ph-design/PH60Slim-Choc/Image/002.jpg

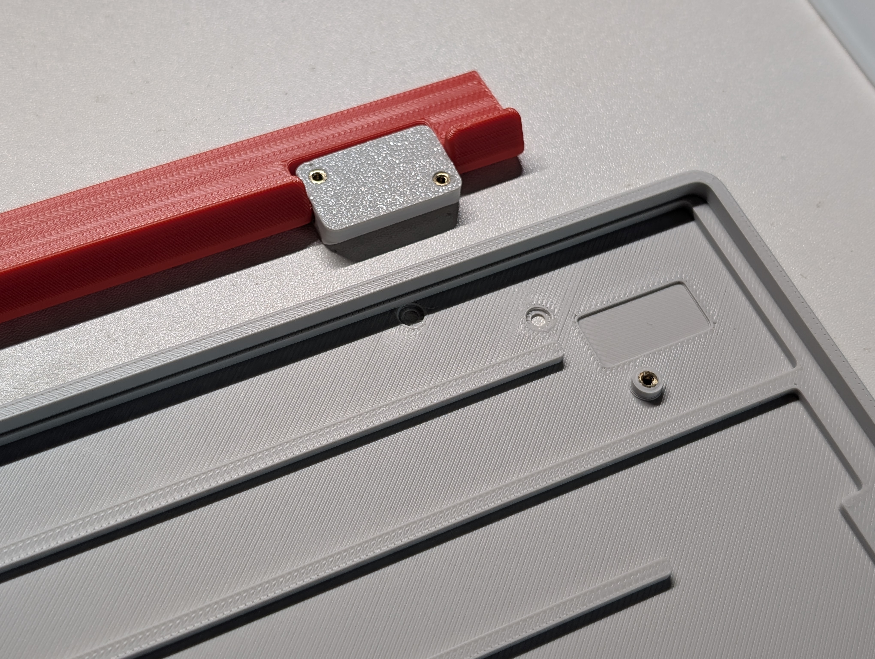
Image/002.jpg
