ph-design/PH60Slim-Choc/Image/009.jpg

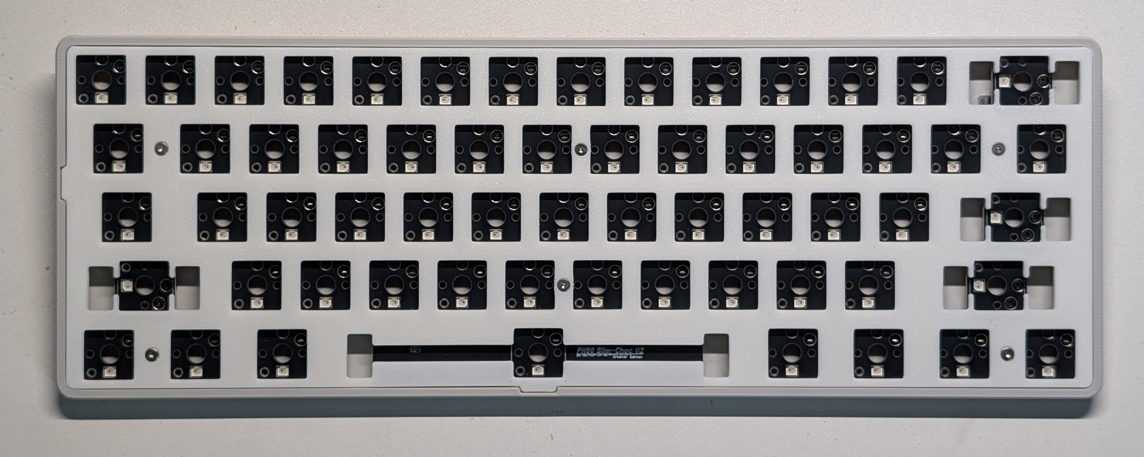
Image/009.jpg
