ph-design/PH60Slim-Choc/Image/010.jpg

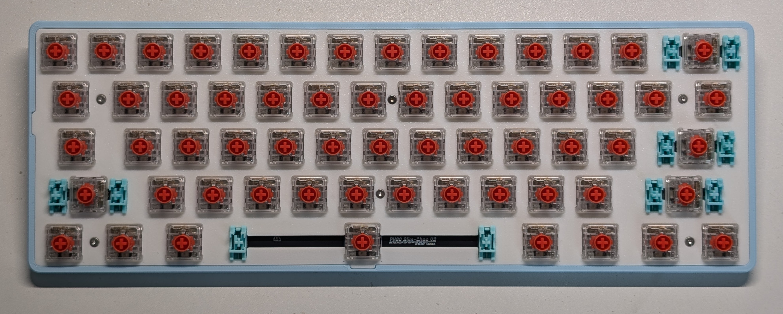
Image/010.jpg
