ph-design/PH60Slim-Choc/PCB/Rev1/PH60Slim-Choc.kicad_sch

## KiCad design PCB/Rev1/PH60Slim-Choc.kicad_sch (2025-04-30)

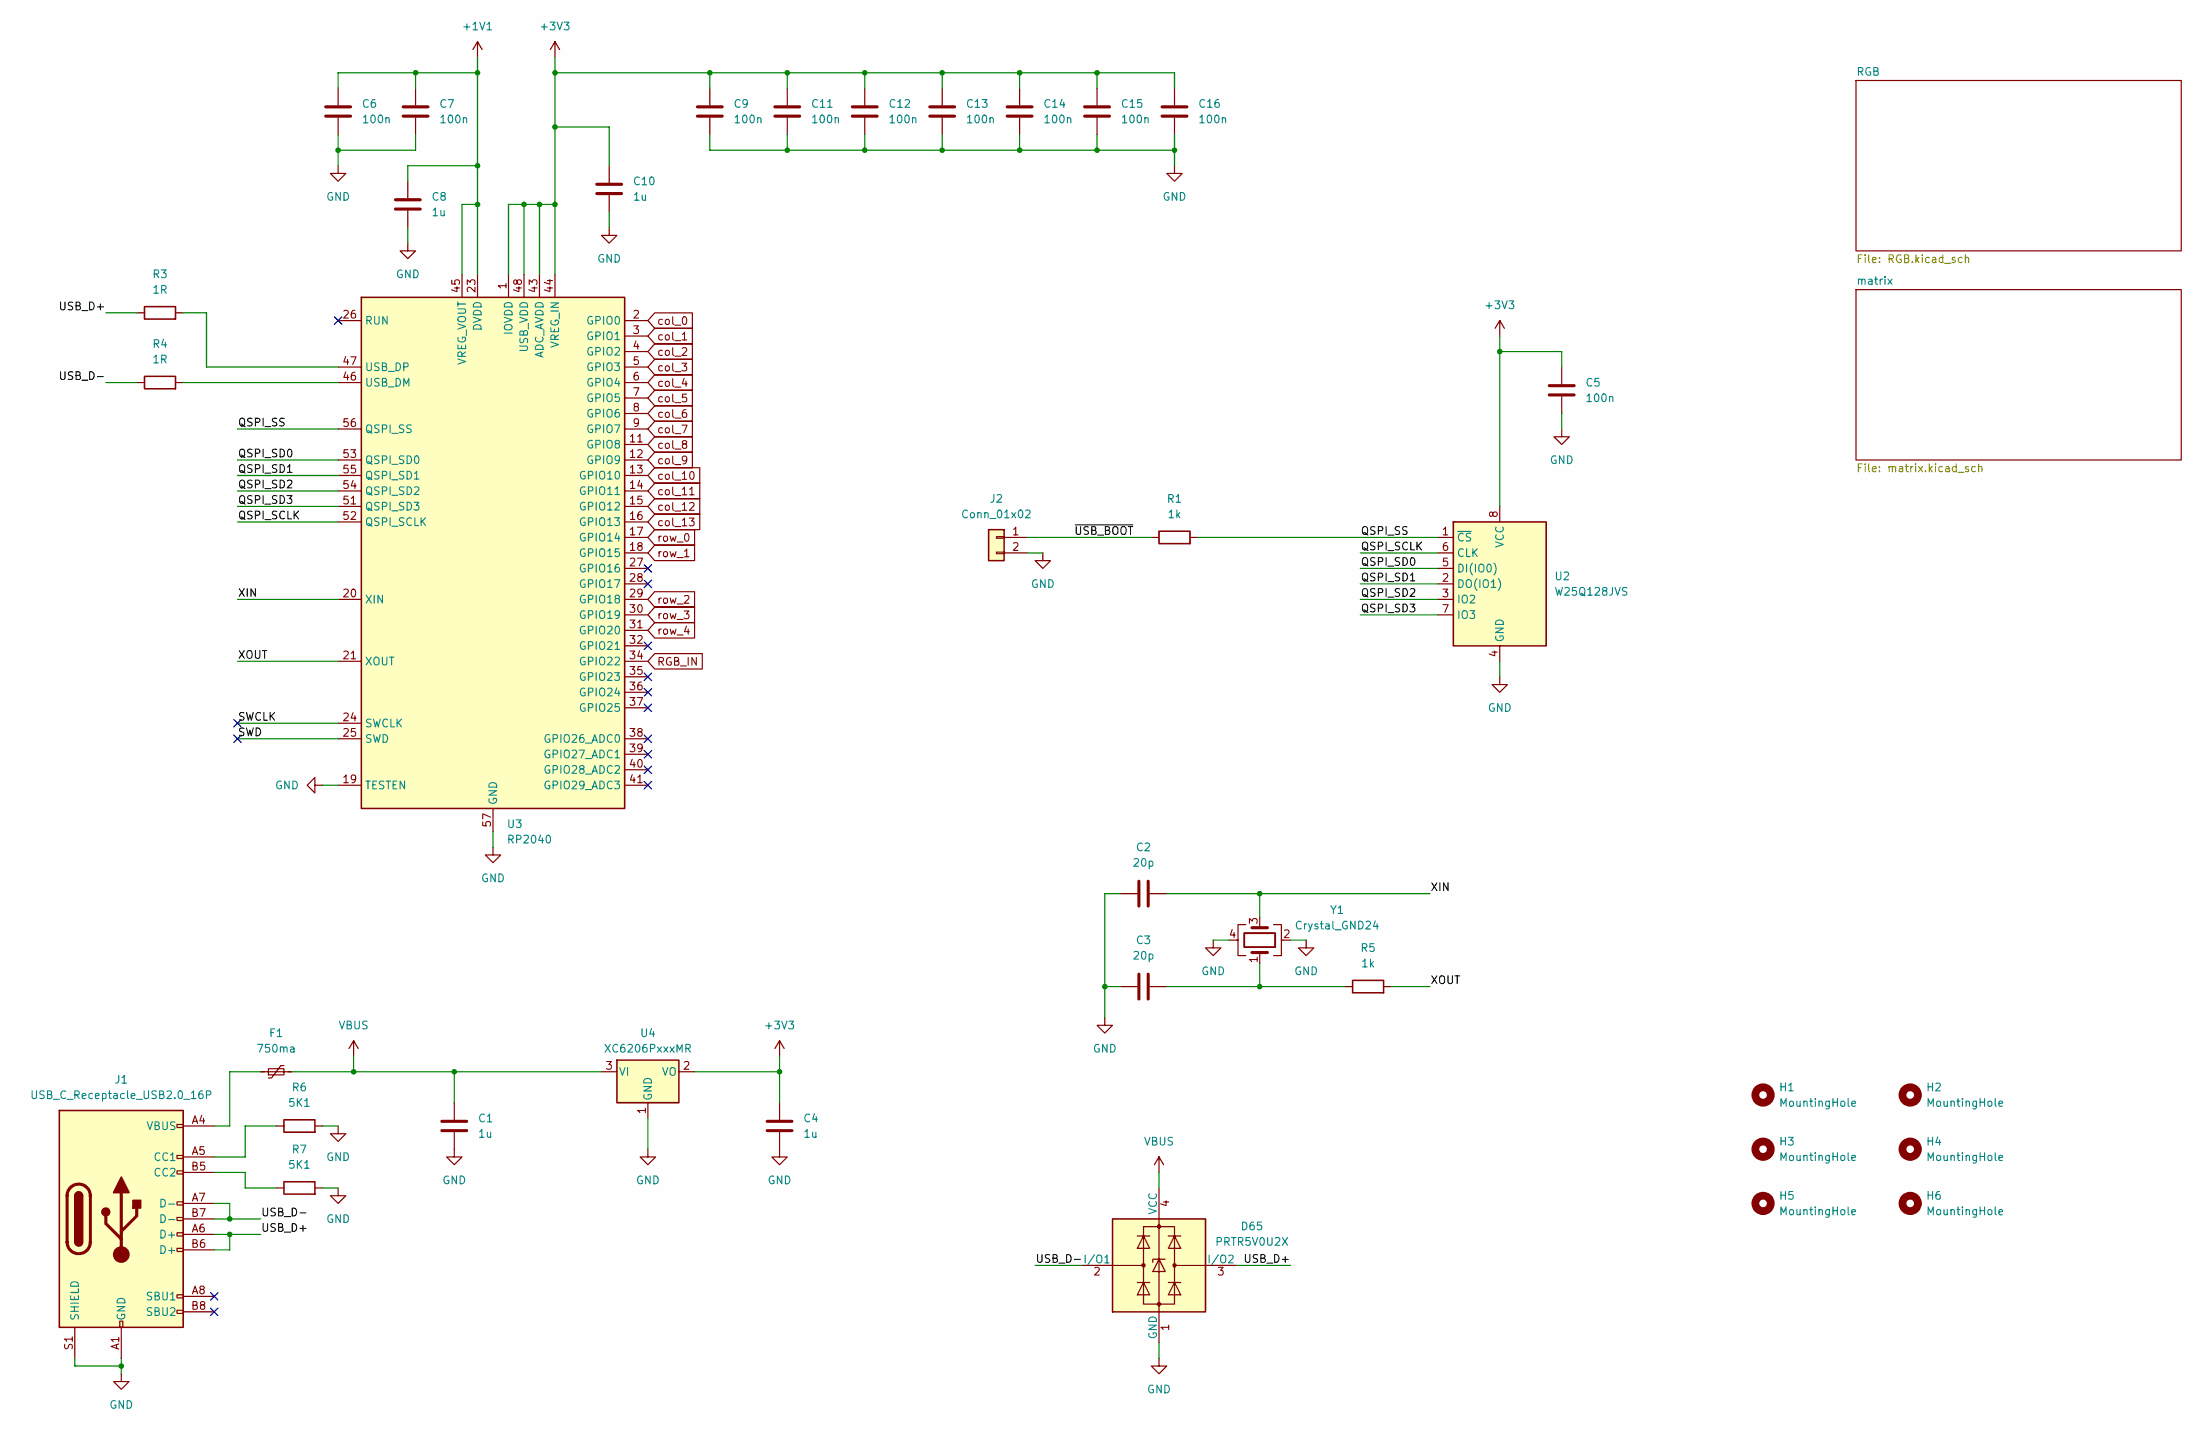
[picture p16: schematic PH60Slim-Choc.kicad_sch]

Parts:
C1, C4, C8, C10: 1u; C_0402_1005Metric
C2, C3: 20p; C_0402_1005Metric
C5, C6, C7, C9, C11, C12, C13, C14, C15, C16: 100n; C_0402_1005Metric
D65: PRTR5V0U2X; SOT-143
F1: 750ma; Fuse_0805_2012Metric
H1, H2, H3, H4, H5, H6: MountingHole; MountingHole_2.2mm_M2
J1: USB_C_Receptacle_USB2.0_16P; USB_C_Receptacle_GCT_USB4105-xx-A_16P_TopMnt_Horizontal
J2: Conn_01x02; PinHeader_1x02_P1.27mm_Vertical
R1, R5: 1k; R_0402_1005Metric
R3, R4: 1R; R_0402_1005Metric
R6, R7: 5K1; R_0402_1005Metric
U2: W25Q128JVS; Winbond_USON-8-1EP_3x2mm_P0.5mm_EP0.2x1.6mm
U3: RP2040; QFN-56-1EP_7x7mm_P0.4mm_EP3.2x3.2mm
U4: XC6206PxxxMR; SOT-23-3
Y1: Crystal_GND24; Crystal_SMD_3225-4Pin_3.2x2.5mm

Connections:
+1V1: C6.1, C7.1, C8.1, U3.23 (DVDD), U3.45 (VREG_VOUT), U3.50 (DVDD)
+3V3: C4.1, C5.1, C9.1, C10.1, C11.1, C12.1, C13.1, C14.1, C15.1, C16.1, U2.8 (VCC), U3.1 (IOVDD), U3.10 (IOVDD), U3.22 (IOVDD), U3.33 (IOVDD), U3.42 (IOVDD), U3.43 (ADC_AVDD), U3.44 (VREG_IN), U3.48 (USB_VDD), U3.49 (IOVDD), U4.2 (VO)
GND: C1.2, C2.2, C3.2, C4.2, C5.2, C6.2, C7.2, C8.2, C9.2, C10.2, C11.2, C12.2, C13.2, C14.2, C15.2, C16.2, D65.1 (GND), J1.A1 (GND), J1.A12 (GND), J1.B1 (GND), J1.B12 (GND), J1.S1 (SHIELD), J2.2, R6.2, R7.2, U2.4 (GND), U3.19 (TESTEN), U3.57 (GND), U4.1 (GND), Y1.2, Y1.4
unnamed: C3.1, R5.1, Y1.1
unnamed: F1.1, J1.A4 (VBUS), J1.A9 (VBUS), J1.B4 (VBUS), J1.B9 (VBUS)
unnamed: J1.A5 (CC1), R6.1
unnamed: J1.B5 (CC2), R7.1
unnamed: R3.2, U3.47 (USB_DP)
unnamed: R4.2, U3.46 (USB_DM)
QSPI_SCLK: U2.6 (CLK), U3.52 (QSPI_SCLK)
QSPI_SD0: U2.5 (DI(IO0)), U3.53 (QSPI_SD0)
QSPI_SD1: U2.2 (DO(IO1)), U3.55 (QSPI_SD1)
QSPI_SD2: U2.3 (IO2), U3.54 (QSPI_SD2)
QSPI_SD3: U2.7 (IO3), U3.51 (QSPI_SD3)
QSPI_SS: R1.2, U2.1 (~CS), U3.56 (QSPI_SS)
RGB_IN: U3.34 (GPIO22)
SWCLK: U3.24 (SWCLK)
SWD: U3.25 (SWD)
USB_D+: D65.3 (I/O2), J1.A6 (D+), J1.B6 (D+), R3.1
USB_D-: D65.2 (I/O1), J1.A7 (D-), J1.B7 (D-), R4.1
VBUS: C1.1, D65.4 (VCC), F1.2, U4.3 (VI)
XIN: C2.1, U3.20 (XIN), Y1.3
XOUT: R5.2, U3.21 (XOUT)
col_0: U3.2 (GPIO0)
col_1: U3.3 (GPIO1)
col_2: U3.4 (GPIO2)
col_3: U3.5 (GPIO3)
col_4: U3.6 (GPIO4)
col_5: U3.7 (GPIO5)
col_6: U3.8 (GPIO6)
col_7: U3.9 (GPIO7)
col_8: U3.11 (GPIO8)
col_9: U3.12 (GPIO9)
col_10: U3.13 (GPIO10)
col_11: U3.14 (GPIO11)
col_12: U3.15 (GPIO12)
col_13: U3.16 (GPIO13)
row_0: U3.17 (GPIO14)
row_1: U3.18 (GPIO15)
row_2: U3.29 (GPIO18)
row_3: U3.30 (GPIO19)
row_4: U3.31 (GPIO20)
~USB_BOOT: J2.1, R1.1
