ph-design/PH60Slim-Choc/PCB/Rev1/RGB.kicad_sch

## KiCad design PCB/Rev1/RGB.kicad_sch (2025-04-30)

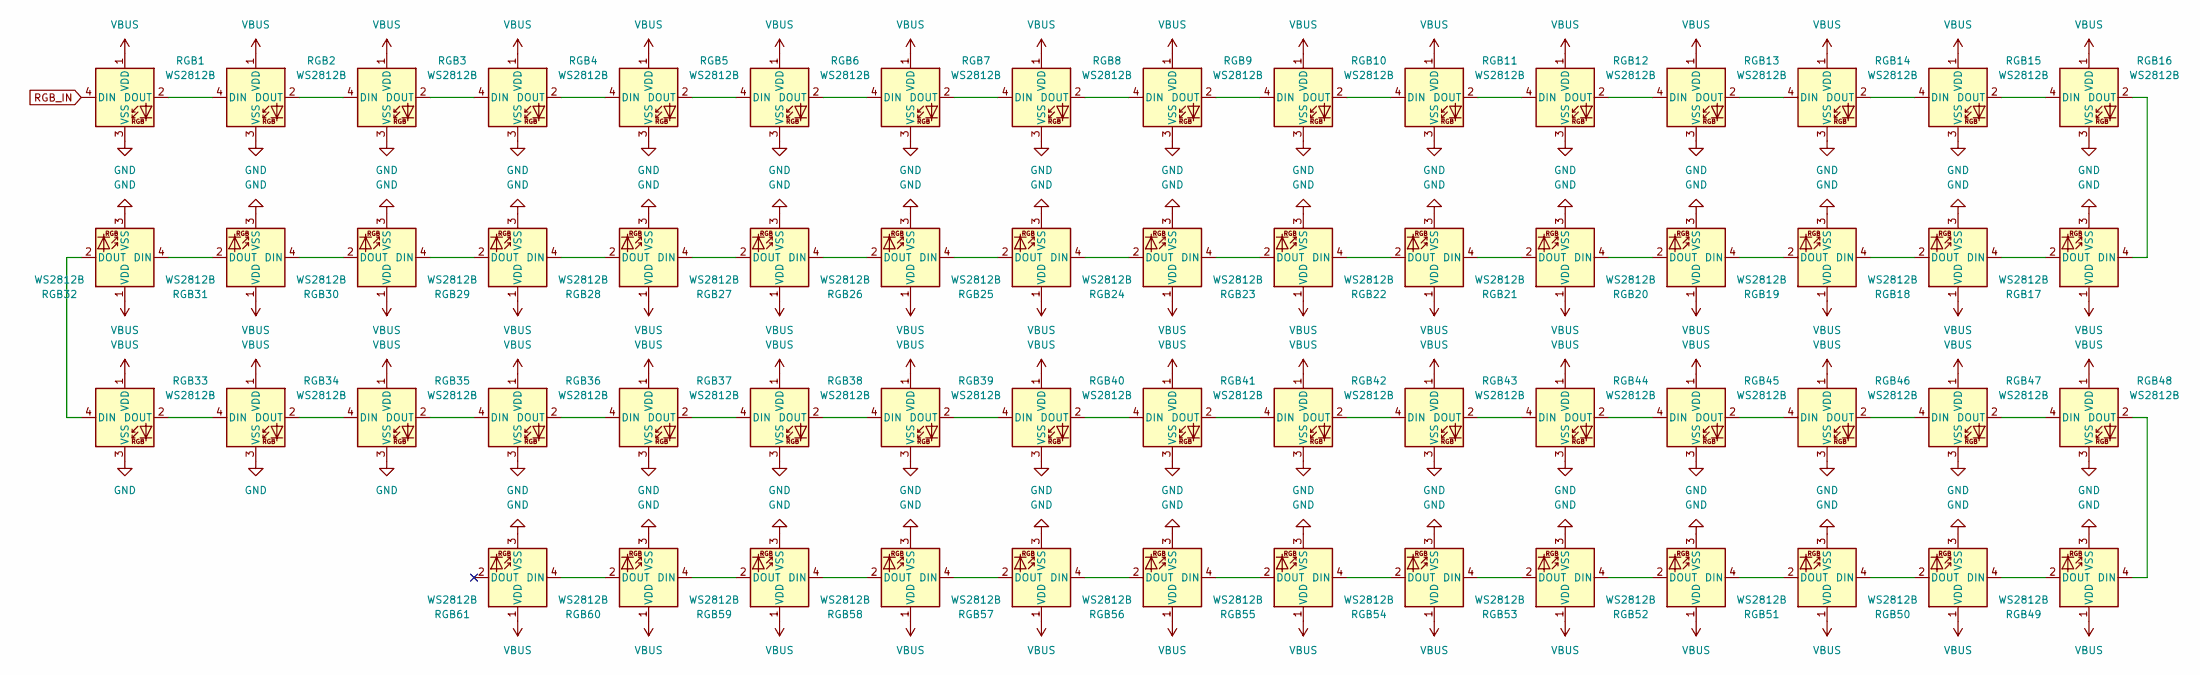
[picture p17: schematic RGB.kicad_sch]

Parts:
RGB1, RGB2, RGB3, RGB4, RGB5, RGB6, RGB7, RGB8, RGB9, RGB10, RGB11, RGB12, RGB13, RGB14, RGB15, RGB16, RGB17, RGB18, RGB19, RGB20, RGB21, RGB22, RGB23, RGB24, RGB25, RGB26, RGB27, RGB28, RGB29, RGB30, RGB31, RGB32, RGB33, RGB34, RGB35, RGB36, RGB37, RGB38, RGB39, RGB40, RGB41, RGB42, RGB43, RGB44, RGB45, RGB46, RGB47, RGB48, RGB49, RGB50, RGB51, RGB52, RGB53, RGB54, RGB55, RGB56, RGB57, RGB58, RGB59, RGB60, RGB61: WS2812B; ws2812B_6028_FIX

Connections:
GND: RGB1.3 (VSS), RGB2.3 (VSS), RGB3.3 (VSS), RGB4.3 (VSS), RGB5.3 (VSS), RGB6.3 (VSS), RGB7.3 (VSS), RGB8.3 (VSS), RGB9.3 (VSS), RGB10.3 (VSS), RGB11.3 (VSS), RGB12.3 (VSS), RGB13.3 (VSS), RGB14.3 (VSS), RGB15.3 (VSS), RGB16.3 (VSS), RGB17.3 (VSS), RGB18.3 (VSS), RGB19.3 (VSS), RGB20.3 (VSS), RGB21.3 (VSS), RGB22.3 (VSS), RGB23.3 (VSS), RGB24.3 (VSS), RGB25.3 (VSS), RGB26.3 (VSS), RGB27.3 (VSS), RGB28.3 (VSS), RGB29.3 (VSS), RGB30.3 (VSS), RGB31.3 (VSS), RGB32.3 (VSS), RGB33.3 (VSS), RGB34.3 (VSS), RGB35.3 (VSS), RGB36.3 (VSS), RGB37.3 (VSS), RGB38.3 (VSS), RGB39.3 (VSS), RGB40.3 (VSS), RGB41.3 (VSS), RGB42.3 (VSS), RGB43.3 (VSS), RGB44.3 (VSS), RGB45.3 (VSS), RGB46.3 (VSS), RGB47.3 (VSS), RGB48.3 (VSS), RGB49.3 (VSS), RGB50.3 (VSS), RGB51.3 (VSS), RGB52.3 (VSS), RGB53.3 (VSS), RGB54.3 (VSS), RGB55.3 (VSS), RGB56.3 (VSS), RGB57.3 (VSS), RGB58.3 (VSS), RGB59.3 (VSS), RGB60.3 (VSS), RGB61.3 (VSS)
unnamed: RGB1.2 (DOUT), RGB2.4 (DIN)
unnamed: RGB2.2 (DOUT), RGB3.4 (DIN)
unnamed: RGB3.2 (DOUT), RGB4.4 (DIN)
unnamed: RGB4.2 (DOUT), RGB5.4 (DIN)
unnamed: RGB5.2 (DOUT), RGB6.4 (DIN)
unnamed: RGB6.2 (DOUT), RGB7.4 (DIN)
unnamed: RGB7.2 (DOUT), RGB8.4 (DIN)
unnamed: RGB8.2 (DOUT), RGB9.4 (DIN)
unnamed: RGB10.2 (DOUT), RGB11.4 (DIN)
unnamed: RGB9.2 (DOUT), RGB10.4 (DIN)
unnamed: RGB11.2 (DOUT), RGB12.4 (DIN)
unnamed: RGB12.2 (DOUT), RGB13.4 (DIN)
unnamed: RGB13.2 (DOUT), RGB14.4 (DIN)
unnamed: RGB14.2 (DOUT), RGB15.4 (DIN)
unnamed: RGB15.2 (DOUT), RGB16.4 (DIN)
unnamed: RGB16.2 (DOUT), RGB17.4 (DIN)
unnamed: RGB17.2 (DOUT), RGB18.4 (DIN)
unnamed: RGB18.2 (DOUT), RGB19.4 (DIN)
unnamed: RGB19.2 (DOUT), RGB20.4 (DIN)
unnamed: RGB20.2 (DOUT), RGB21.4 (DIN)
unnamed: RGB21.2 (DOUT), RGB22.4 (DIN)
unnamed: RGB22.2 (DOUT), RGB23.4 (DIN)
unnamed: RGB23.2 (DOUT), RGB24.4 (DIN)
unnamed: RGB24.2 (DOUT), RGB25.4 (DIN)
unnamed: RGB25.2 (DOUT), RGB26.4 (DIN)
unnamed: RGB26.2 (DOUT), RGB27.4 (DIN)
unnamed: RGB27.2 (DOUT), RGB28.4 (DIN)
unnamed: RGB28.2 (DOUT), RGB29.4 (DIN)
unnamed: RGB29.2 (DOUT), RGB30.4 (DIN)
unnamed: RGB30.2 (DOUT), RGB31.4 (DIN)
unnamed: RGB31.2 (DOUT), RGB32.4 (DIN)
unnamed: RGB32.2 (DOUT), RGB33.4 (DIN)
unnamed: RGB33.2 (DOUT), RGB34.4 (DIN)
unnamed: RGB34.2 (DOUT), RGB35.4 (DIN)
unnamed: RGB35.2 (DOUT), RGB36.4 (DIN)
unnamed: RGB36.2 (DOUT), RGB37.4 (DIN)
unnamed: RGB37.2 (DOUT), RGB38.4 (DIN)
unnamed: RGB38.2 (DOUT), RGB39.4 (DIN)
unnamed: RGB39.2 (DOUT), RGB40.4 (DIN)
unnamed: RGB40.2 (DOUT), RGB41.4 (DIN)
unnamed: RGB41.2 (DOUT), RGB42.4 (DIN)
unnamed: RGB42.2 (DOUT), RGB43.4 (DIN)
unnamed: RGB43.2 (DOUT), RGB44.4 (DIN)
unnamed: RGB44.2 (DOUT), RGB45.4 (DIN)
unnamed: RGB45.2 (DOUT), RGB46.4 (DIN)
unnamed: RGB46.2 (DOUT), RGB47.4 (DIN)
unnamed: RGB47.2 (DOUT), RGB48.4 (DIN)
unnamed: RGB48.2 (DOUT), RGB49.4 (DIN)
unnamed: RGB49.2 (DOUT), RGB50.4 (DIN)
unnamed: RGB50.2 (DOUT), RGB51.4 (DIN)
unnamed: RGB51.2 (DOUT), RGB52.4 (DIN)
unnamed: RGB52.2 (DOUT), RGB53.4 (DIN)
unnamed: RGB53.2 (DOUT), RGB54.4 (DIN)
unnamed: RGB54.2 (DOUT), RGB55.4 (DIN)
unnamed: RGB55.2 (DOUT), RGB56.4 (DIN)
unnamed: RGB56.2 (DOUT), RGB57.4 (DIN)
unnamed: RGB57.2 (DOUT), RGB58.4 (DIN)
unnamed: RGB58.2 (DOUT), RGB59.4 (DIN)
unnamed: RGB59.2 (DOUT), RGB60.4 (DIN)
unnamed: RGB60.2 (DOUT), RGB61.4 (DIN)
RGB_IN: RGB1.4 (DIN)
VBUS: RGB1.1 (VDD), RGB2.1 (VDD), RGB3.1 (VDD), RGB4.1 (VDD), RGB5.1 (VDD), RGB6.1 (VDD), RGB7.1 (VDD), RGB8.1 (VDD), RGB9.1 (VDD), RGB10.1 (VDD), RGB11.1 (VDD), RGB12.1 (VDD), RGB13.1 (VDD), RGB14.1 (VDD), RGB15.1 (VDD), RGB16.1 (VDD), RGB17.1 (VDD), RGB18.1 (VDD), RGB19.1 (VDD), RGB20.1 (VDD), RGB21.1 (VDD), RGB22.1 (VDD), RGB23.1 (VDD), RGB24.1 (VDD), RGB25.1 (VDD), RGB26.1 (VDD), RGB27.1 (VDD), RGB28.1 (VDD), RGB29.1 (VDD), RGB30.1 (VDD), RGB31.1 (VDD), RGB32.1 (VDD), RGB33.1 (VDD), RGB34.1 (VDD), RGB35.1 (VDD), RGB36.1 (VDD), RGB37.1 (VDD), RGB38.1 (VDD), RGB39.1 (VDD), RGB40.1 (VDD), RGB41.1 (VDD), RGB42.1 (VDD), RGB43.1 (VDD), RGB44.1 (VDD), RGB45.1 (VDD), RGB46.1 (VDD), RGB47.1 (VDD), RGB48.1 (VDD), RGB49.1 (VDD), RGB50.1 (VDD), RGB51.1 (VDD), RGB52.1 (VDD), RGB53.1 (VDD), RGB54.1 (VDD), RGB55.1 (VDD), RGB56.1 (VDD), RGB57.1 (VDD), RGB58.1 (VDD), RGB59.1 (VDD), RGB60.1 (VDD), RGB61.1 (VDD)
